jessiepullaro414/Cluster/gauges/ClusterGauges_back.png

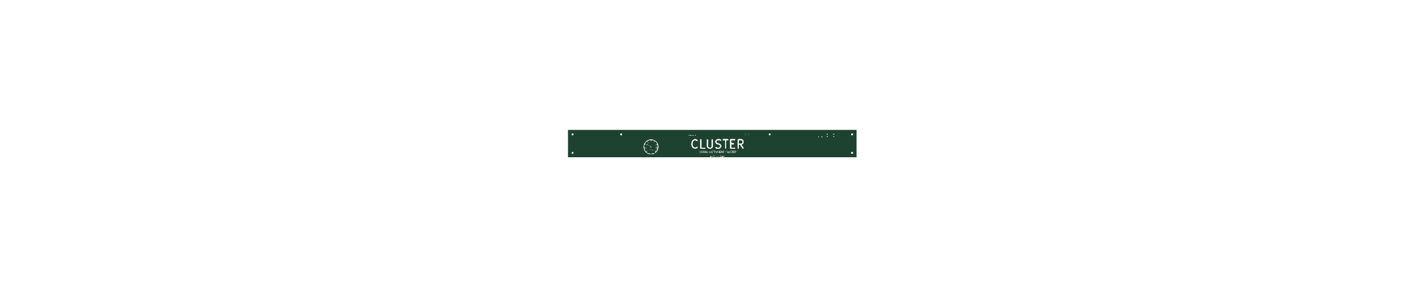
gauges/ClusterGauges_back.png
